cryptoadvance/specter-diy/docs/pictures/kit_with_case.jpg

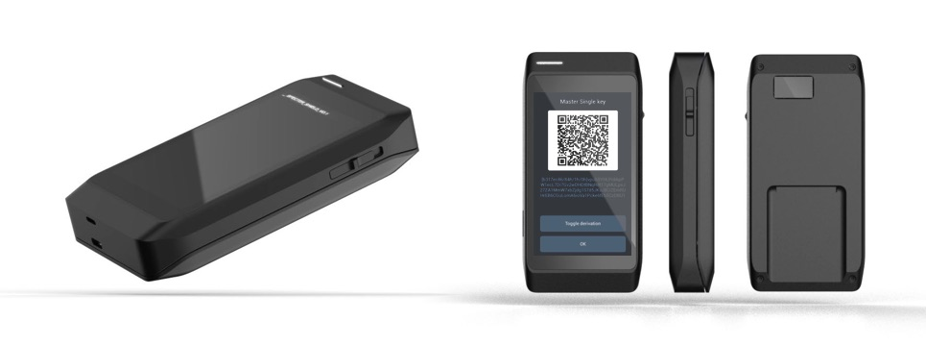
docs/pictures/kit_with_case.jpg
