cryptoadvance/specter-diy/shield/Alternative_3D_Printed_Case/06_Spacer.stl

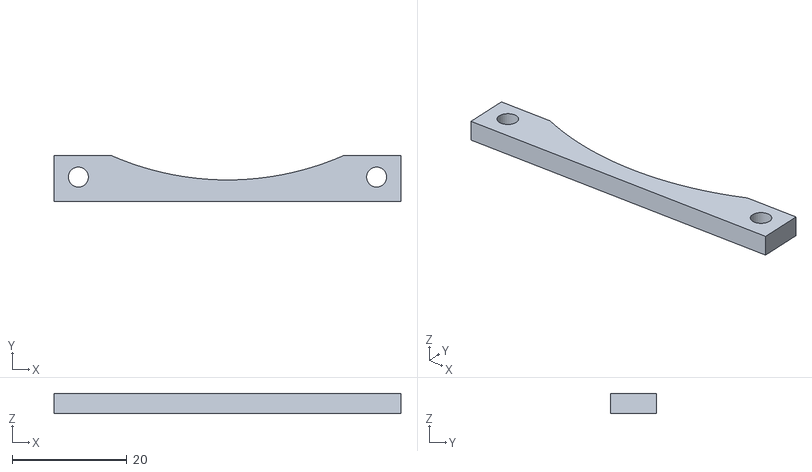
[picture p65: CAD file, 2021-03-23]
shield/Alternative_3D_Printed_Case/06_Spacer.stl
60.5 x 8.00 x 3.50
