cryptoadvance/specter-diy/shield/Alternative_3D_Printed_Case/05_Button.stl

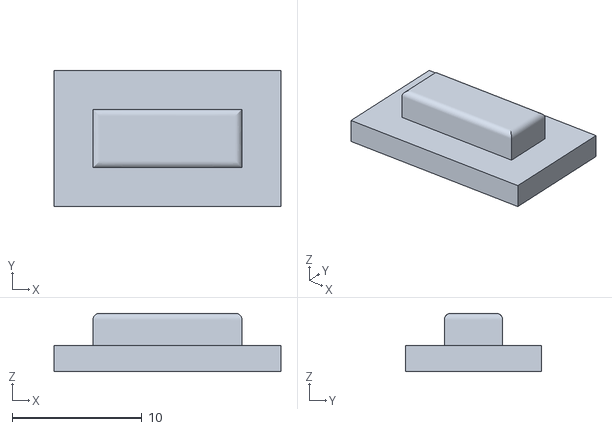
[picture p66: CAD file, 2021-03-23]
shield/Alternative_3D_Printed_Case/05_Button.stl
17.5 x 10.5 x 4.50
