cryptoadvance/specter-diy/simulate.py

import sys
sys.path.append('./src')
sys.path.append('./f469-disco/libs/common')
sys.path.append('./f469-disco/libs/unix')
sys.path.append('./f469-disco/usermods/udisplay_f469/display_unixport')

import main

main.main()
